telzo2000/cool844V2/img/img00001.jpg

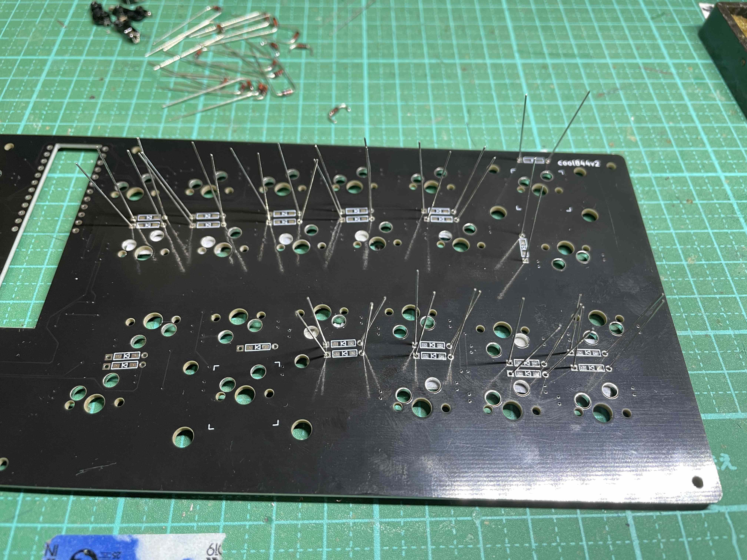
img/img00001.jpg
