telzo2000/cool844V2/img/img00002.jpg

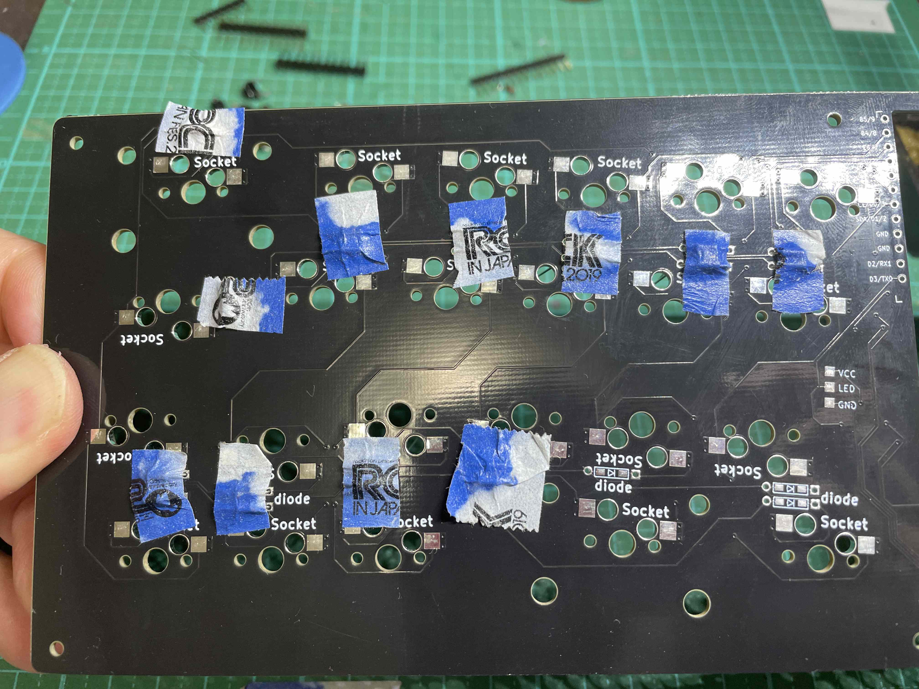
img/img00002.jpg
