telzo2000/cool844V2/img/img00006.jpg

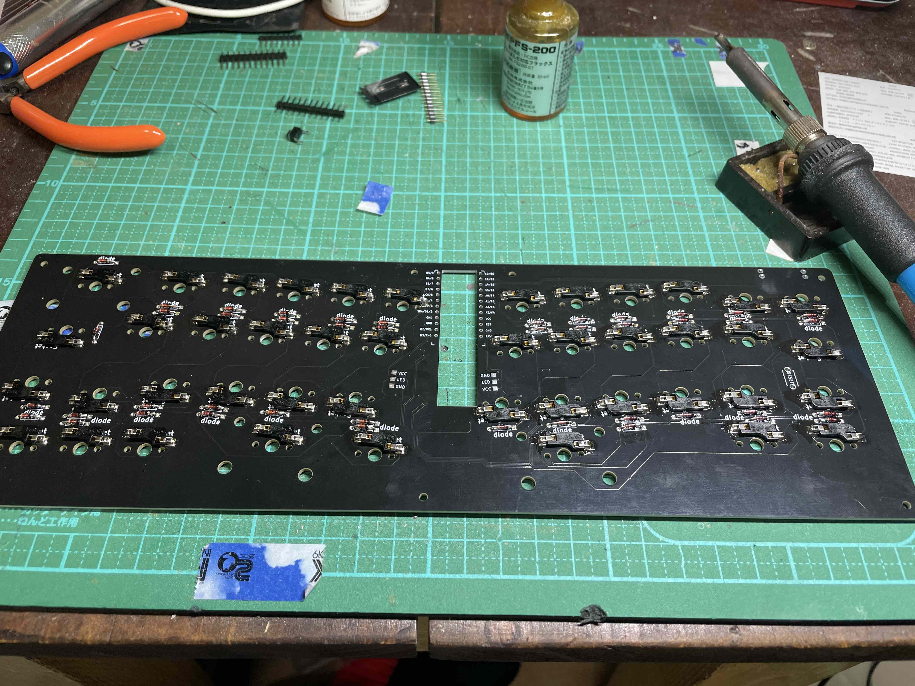
img/img00006.jpg
