telzo2000/cool844V2/img/img00007.jpg

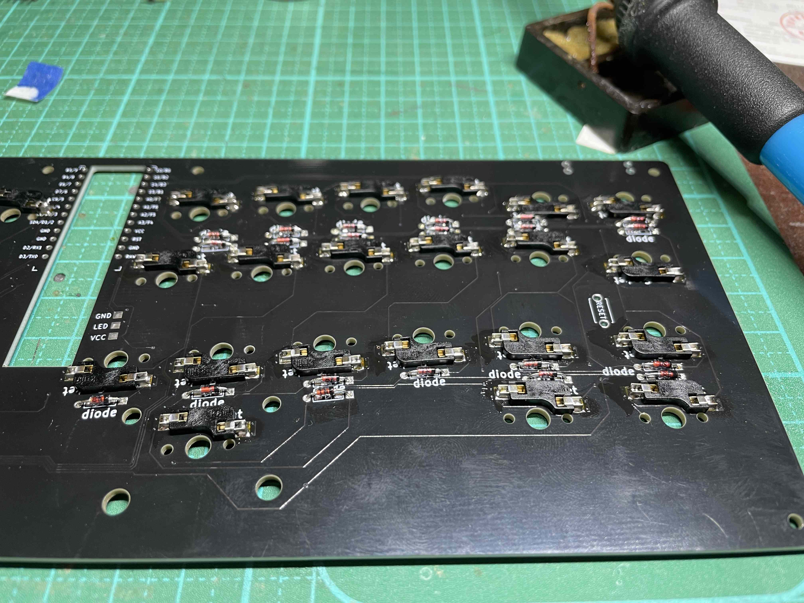
img/img00007.jpg
