telzo2000/cool844V2/img/img00023.jpg

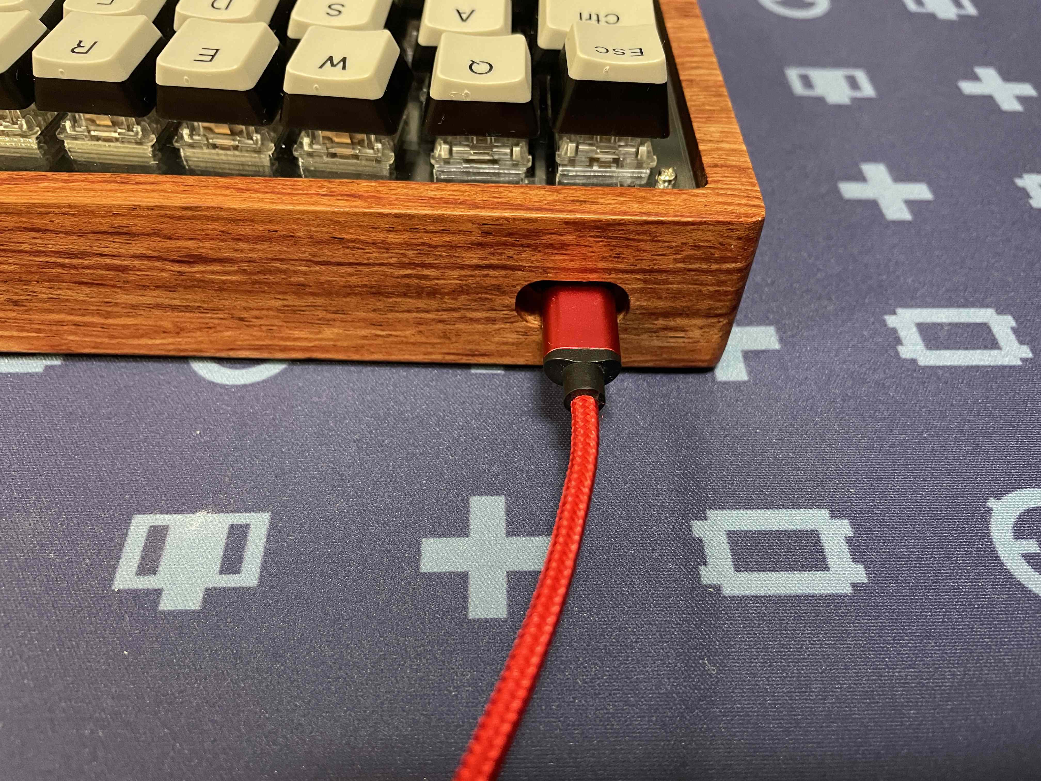
img/img00023.jpg
