telzo2000/cool844V2/img/img00045.jpg

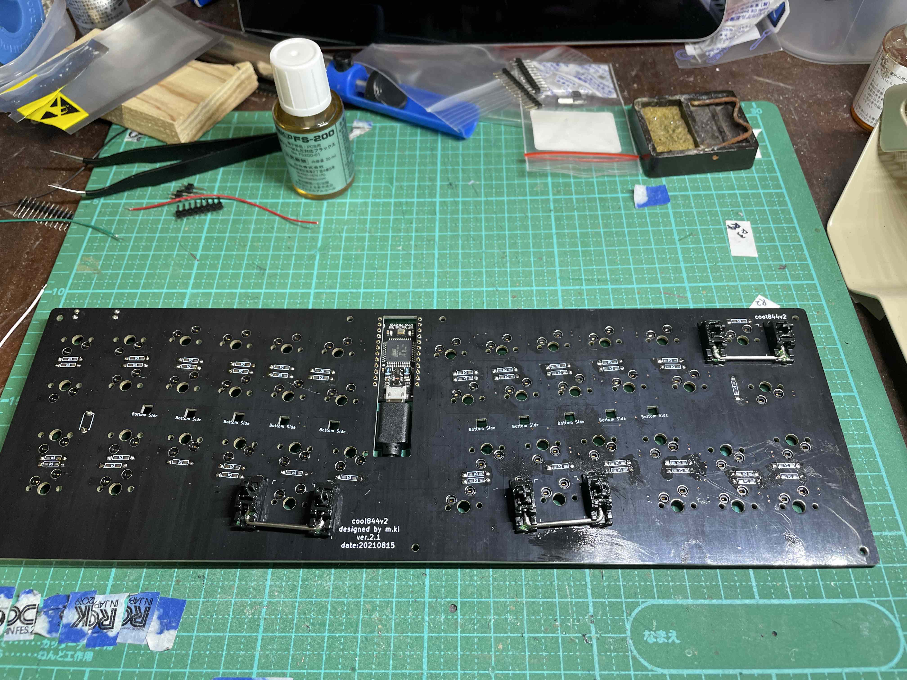
img/img00045.jpg
