telzo2000/cool844V2/img/img00071.jpg

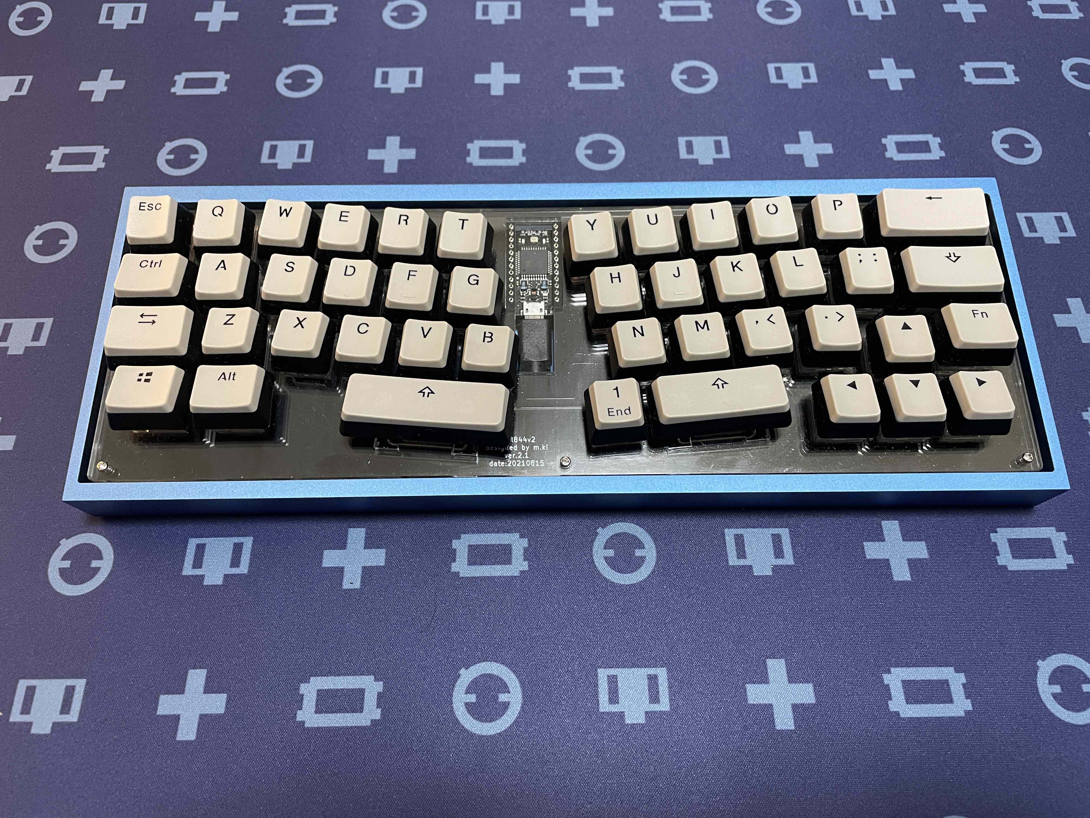
img/img00071.jpg
